nakioman/retro-pc/hardware/mac-classic-case/stl/eject-cap.stl

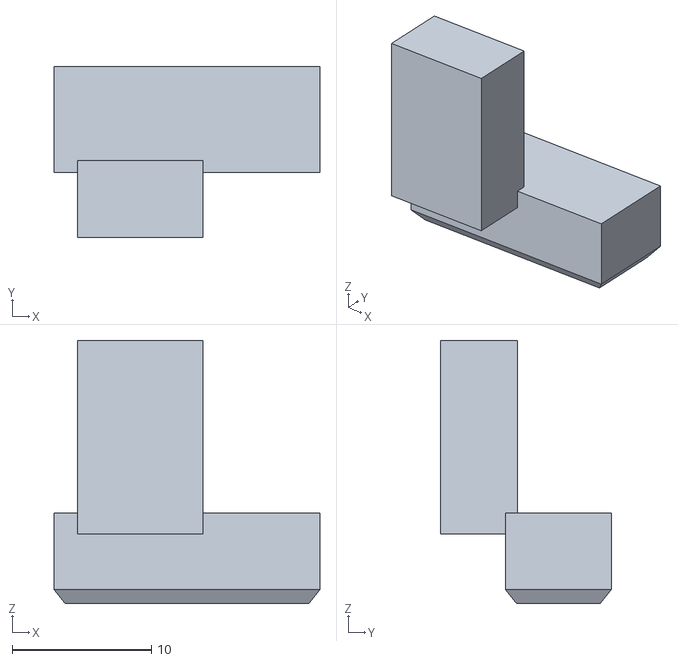
[picture p22: CAD file, 2026-09-06]
hardware/mac-classic-case/stl/eject-cap.stl
19.1 x 12.2 x 18.9
