nakioman/retro-pc/hardware/mac-classic-case/stl/cage-pedestals.stl

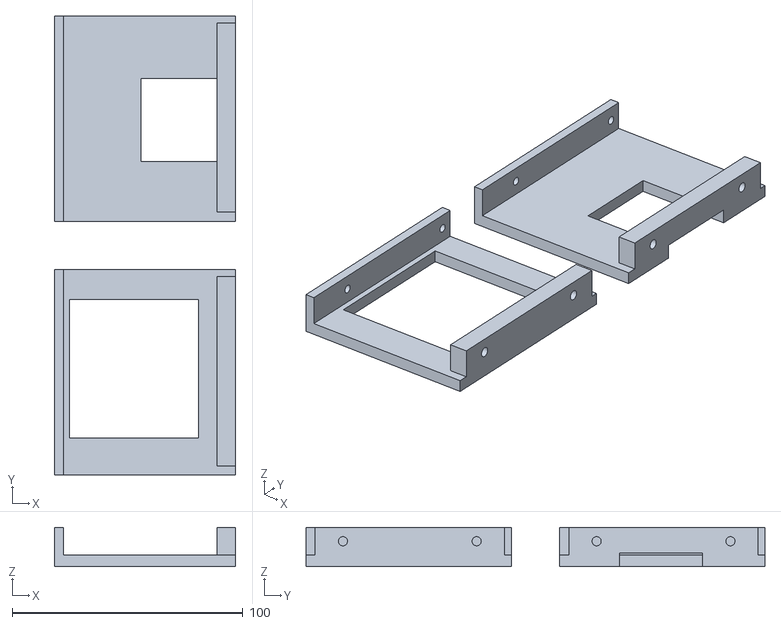
[picture p23: CAD file, 2026-09-06]
hardware/mac-classic-case/stl/cage-pedestals.stl
78.6 x 199.0 x 17.0
