nakioman/retro-pc/hardware/mac-classic-case/stl/hdd-cradle.stl

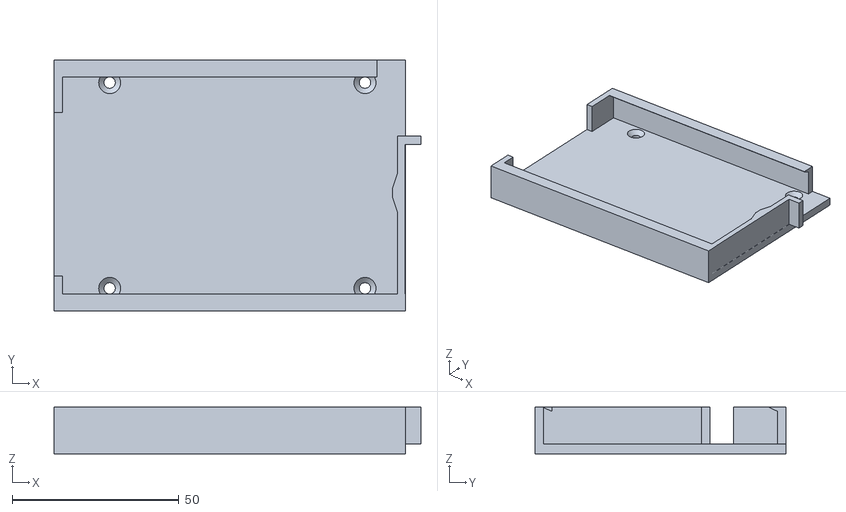
[picture p24: CAD file, 2026-09-06]
hardware/mac-classic-case/stl/hdd-cradle.stl
110.1 x 75.3 x 14.0
