nakioman/retro-pc/hardware/mac-classic-case/stl/back-upper-right.stl

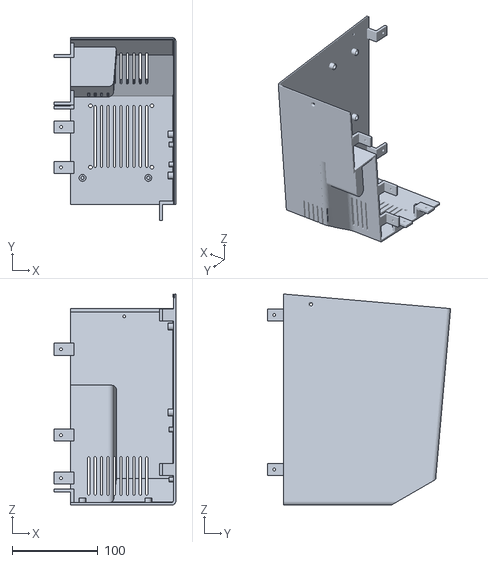
[picture p25: CAD file, 2026-09-06]
hardware/mac-classic-case/stl/back-upper-right.stl
141.6 x 213.4 x 245.6
