nakioman/retro-pc/appliance/installer/payload/profiles/386sx16/86box.cfg

[Trident TVGA 8900 #1]
bios = tvga8900b
memory = 512

[General]
vid_renderer = sdl
mouse_auto_capture = 1
start_in_fullscreen = 1
floppy_control_socket_enabled = 1
floppy_control_socket_path = /run/retrobox/86box-floppy.sock
gpio_active_low = 1
gpio_enabled = 1
gpio_hdd_pin = 360
gpio_device = /dev/gpiochip0

[GL3 Shaders]
shaders = 1
shader0 = /opt/86Box/shaders/crt/crt-easymode.glslp

[GL3 Shaders - crt-easymode.glslp]
SCANLINE_CUTOFF = 900
SCANLINE_BRIGHT_MIN = 0.30
SCANLINE_BRIGHT_MAX = 0.65
MASK_SIZE = 3
MASK_STRENGTH = 0.35
MASK_STAGGER = 3
MASK_DOT_HEIGHT = 2
SHARPNESS_H = 0.7
GAMMA_INPUT = 2.4
BRIGHT_BOOST = 1.3

[Machine]
cpu_family = i386sx
cpu_multi = 1
cpu_speed = 16000000
cpu_use_dynarec = 0
machine = awardsx
mem_size = 2048

[Video]
gfxcard = tvga8900

[Input devices]
keyboard_type = keyboard_at
mouse_type = msserial

[Network]
net_01_link = 0
net_02_link = 0
net_03_link = 0
net_04_link = 0

[Storage controllers]
hdc_1 = ide_isa

[Hard disks]
hdd_01_fn = hdd.raw
hdd_01_ide_channel = 0:0
hdd_01_parameters = 39, 4, 762, 0, ide
hdd_01_speed = CP30064

[Floppy and CD-ROM drives]
fdd_01_audio = alps_df354h148f_80t
fdd_01_type = 35_2hd
fdd_02_type = none
fdd_host_buffering = 1
